josuegaleas/JayK/Firmware/config.h

/*
 * Author: Josue Galeas
 * Last Edit: 2019.11.09
 */

#ifndef CONFIG_H
#define CONFIG_H

#define VENDOR_ID 0xDEAD
#define PRODUCT_ID 0x0001
#define DEVICE_VER 0x0002
#define MANUFACTURER Josue Galeas
#define PRODUCT JayK
#define DESCRIPTION Firmware for JayK

#define MATRIX_ROWS 5
#define MATRIX_COLS 21
#define MATRIX_HAS_GHOST

#endif /* CONFIG_H */
